whitelynx/dactyl-lynx-keyboard/things/dactyl-lynx-6x5-left-finger.stl

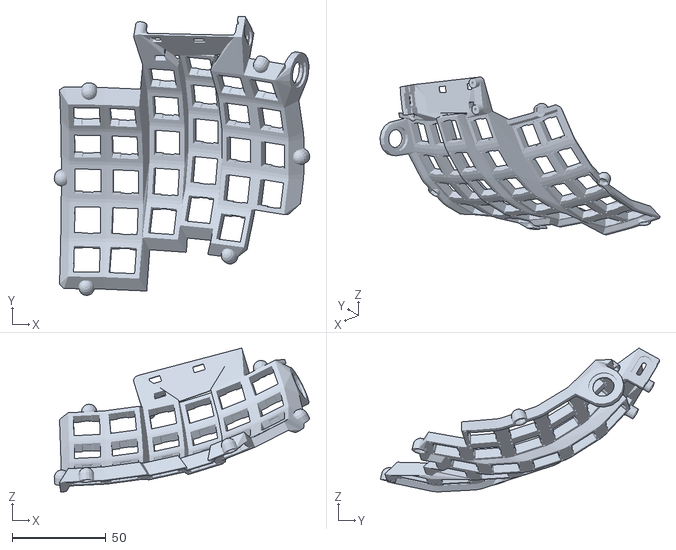
[picture p14: CAD file, 2024-12-01]
things/dactyl-lynx-6x5-left-finger.stl
136.0 x 148.5 x 76.6
