whitelynx/dactyl-lynx-keyboard/things/dactyl-lynx-6x5-left-bottom-with-feet-tripod.scad

include </home/whitelynx/.local/share/virtualenvs/dactyl-lynx-keyboard-vn24Ws0r/lib/python3.12/site-packages/solid2/extensions/bosl2/BOSL2/version.scad>;
include </home/whitelynx/.local/share/virtualenvs/dactyl-lynx-keyboard-vn24Ws0r/lib/python3.12/site-packages/solid2/extensions/bosl2/BOSL2/constants.scad>;
include </home/whitelynx/.local/share/virtualenvs/dactyl-lynx-keyboard-vn24Ws0r/lib/python3.12/site-packages/solid2/extensions/bosl2/BOSL2/transforms.scad>;
include </home/whitelynx/.local/share/virtualenvs/dactyl-lynx-keyboard-vn24Ws0r/lib/python3.12/site-packages/solid2/extensions/bosl2/BOSL2/distributors.scad>;
include </home/whitelynx/.local/share/virtualenvs/dactyl-lynx-keyboard-vn24Ws0r/lib/python3.12/site-packages/solid2/extensions/bosl2/BOSL2/mutators.scad>;
include </home/whitelynx/.local/share/virtualenvs/dactyl-lynx-keyboard-vn24Ws0r/lib/python3.12/site-packages/solid2/extensions/bosl2/BOSL2/color.scad>;
include </home/whitelynx/.local/share/virtualenvs/dactyl-lynx-keyboard-vn24Ws0r/lib/python3.12/site-packages/solid2/extensions/bosl2/BOSL2/attachments.scad>;
include </home/whitelynx/.local/share/virtualenvs/dactyl-lynx-keyboard-vn24Ws0r/lib/python3.12/site-packages/solid2/extensions/bosl2/BOSL2/shapes3d.scad>;
include </home/whitelynx/.local/share/virtualenvs/dactyl-lynx-keyboard-vn24Ws0r/lib/python3.12/site-packages/solid2/extensions/bosl2/BOSL2/shapes2d.scad>;
include </home/whitelynx/.local/share/virtualenvs/dactyl-lynx-keyboard-vn24Ws0r/lib/python3.12/site-packages/solid2/extensions/bosl2/BOSL2/drawing.scad>;
include </home/whitelynx/.local/share/virtualenvs/dactyl-lynx-keyboard-vn24Ws0r/lib/python3.12/site-packages/solid2/extensions/bosl2/BOSL2/masks3d.scad>;
include </home/whitelynx/.local/share/virtualenvs/dactyl-lynx-keyboard-vn24Ws0r/lib/python3.12/site-packages/solid2/extensions/bosl2/BOSL2/masks2d.scad>;
include </home/whitelynx/.local/share/virtualenvs/dactyl-lynx-keyboard-vn24Ws0r/lib/python3.12/site-packages/solid2/extensions/bosl2/BOSL2/math.scad>;
include </home/whitelynx/.local/share/virtualenvs/dactyl-lynx-keyboard-vn24Ws0r/lib/python3.12/site-packages/solid2/extensions/bosl2/BOSL2/paths.scad>;
include </home/whitelynx/.local/share/virtualenvs/dactyl-lynx-keyboard-vn24Ws0r/lib/python3.12/site-packages/solid2/extensions/bosl2/BOSL2/lists.scad>;
include </home/whitelynx/.local/share/virtualenvs/dactyl-lynx-keyboard-vn24Ws0r/lib/python3.12/site-packages/solid2/extensions/bosl2/BOSL2/comparisons.scad>;
include </home/whitelynx/.local/share/virtualenvs/dactyl-lynx-keyboard-vn24Ws0r/lib/python3.12/site-packages/solid2/extensions/bosl2/BOSL2/linalg.scad>;
include </home/whitelynx/.local/share/virtualenvs/dactyl-lynx-keyboard-vn24Ws0r/lib/python3.12/site-packages/solid2/extensions/bosl2/BOSL2/trigonometry.scad>;
include </home/whitelynx/.local/share/virtualenvs/dactyl-lynx-keyboard-vn24Ws0r/lib/python3.12/site-packages/solid2/extensions/bosl2/BOSL2/vectors.scad>;
include </home/whitelynx/.local/share/virtualenvs/dactyl-lynx-keyboard-vn24Ws0r/lib/python3.12/site-packages/solid2/extensions/bosl2/BOSL2/affine.scad>;
include </home/whitelynx/.local/share/virtualenvs/dactyl-lynx-keyboard-vn24Ws0r/lib/python3.12/site-packages/solid2/extensions/bosl2/BOSL2/coords.scad>;
include </home/whitelynx/.local/share/virtualenvs/dactyl-lynx-keyboard-vn24Ws0r/lib/python3.12/site-packages/solid2/extensions/bosl2/BOSL2/geometry.scad>;
include </home/whitelynx/.local/share/virtualenvs/dactyl-lynx-keyboard-vn24Ws0r/lib/python3.12/site-packages/solid2/extensions/bosl2/BOSL2/regions.scad>;
include </home/whitelynx/.local/share/virtualenvs/dactyl-lynx-keyboard-vn24Ws0r/lib/python3.12/site-packages/solid2/extensions/bosl2/BOSL2/strings.scad>;
include </home/whitelynx/.local/share/virtualenvs/dactyl-lynx-keyboard-vn24Ws0r/lib/python3.12/site-packages/solid2/extensions/bosl2/BOSL2/skin.scad>;
include </home/whitelynx/.local/share/virtualenvs/dactyl-lynx-keyboard-vn24Ws0r/lib/python3.12/site-packages/solid2/extensions/bosl2/BOSL2/vnf.scad>;
include </home/whitelynx/.local/share/virtualenvs/dactyl-lynx-keyboard-vn24Ws0r/lib/python3.12/site-packages/solid2/extensions/bosl2/BOSL2/utility.scad>;
include </home/whitelynx/.local/share/virtualenvs/dactyl-lynx-keyboard-vn24Ws0r/lib/python3.12/site-packages/solid2/extensions/bosl2/BOSL2/partitions.scad>;
include </home/whitelynx/.local/share/virtualenvs/dactyl-lynx-keyboard-vn24Ws0r/lib/python3.12/site-packages/solid2/extensions/bosl2/BOSL2/screws.scad>;

union() {
	mirror(v = [1, 0, 0]) {
		union() {
			difference() {
				union() {
					difference() {
						union() {
							translate(v = [0, 0, 30.5]) {
								rotate(a = 18.0, v = [1, 0, 0]) {
									rotate(a = 18.0, v = [0, 1, 0]) {
										translate(v = [0, 0, 3]) {
											translate(v = [0, 0, 230.49306344750678]) {
												rotate(a = 10.0, v = [0, 1, 0]) {
													translate(v = [0, 0, -230.49306344750678]) {
														translate(v = [0, 0, 79.73635378597841]) {
															rotate(a = 29.999999999999996, v = [1, 0, 0]) {
																translate(v = [0, 0, -79.73635378597841]) {
																	translate(v = [0, 0, -12.5]) {
																		cube(center = true, size = [20.0, 20.0, 3]);
																	}
																}
															}
														}
													}
												}
											}
										}
									}
								}
							}
							translate(v = [0, 0, 30.5]) {
								rotate(a = 18.0, v = [1, 0, 0]) {
									rotate(a = 18.0, v = [0, 1, 0]) {
										translate(v = [0, 0, 3]) {
											translate(v = [0, 0, 230.49306344750678]) {
												rotate(a = 5.0, v = [0, 1, 0]) {
													translate(v = [0, 0, -230.49306344750678]) {
														translate(v = [0, 0, 79.73635378597841]) {
															rotate(a = 29.999999999999996, v = [1, 0, 0]) {
																translate(v = [0, 0, -79.73635378597841]) {
																	translate(v = [-2, 0, -12.5]) {
																		cube(center = true, size = [20.0, 20.0, 3]);
																	}
																}
															}
														}
													}
												}
											}
										}
									}
								}
							}
							translate(v = [0, 0, 30.5]) {
								rotate(a = 18.0, v = [1, 0, 0]) {
									rotate(a = 18.0, v = [0, 1, 0]) {
										translate(v = [0, 0, 3]) {
											translate(v = [0, 6.82, -4.0]) {
												translate(v = [0, 0, 230.49306344750678]) {
													rotate(a = 0.0, v = [0, 1, 0]) {
														translate(v = [0, 0, -230.49306344750678]) {
															translate(v = [0, 0, 79.73635378597841]) {
																rotate(a = 29.999999999999996, v = [1, 0, 0]) {
																	translate(v = [0, 0, -79.73635378597841]) {
																		translate(v = [0, 0, -12.5]) {
																			cube(center = true, size = [22.0, 20.0, 3]);
																		}
																	}
																}
															}
														}
													}
												}
											}
										}
									}
								}
							}
							translate(v = [0, 0, 30.5]) {
								rotate(a = 18.0, v = [1, 0, 0]) {
									rotate(a = 18.0, v = [0, 1, 0]) {
										translate(v = [0, 0, 3]) {
											translate(v = [0, 0, 230.49306344750678]) {
												rotate(a = -5.0, v = [0, 1, 0]) {
													translate(v = [0, 0, -230.49306344750678]) {
														translate(v = [0, 0, 79.73635378597841]) {
															rotate(a = 29.999999999999996, v = [1, 0, 0]) {
																translate(v = [0, 0, -79.73635378597841]) {
																	translate(v = [2, 0, -12.5]) {
																		cube(center = true, size = [20.0, 20.0, 3]);
																	}
																}
															}
														}
													}
												}
											}
										}
									}
								}
							}
							translate(v = [0, 0, 30.5]) {
								rotate(a = 18.0, v = [1, 0, 0]) {
									rotate(a = 18.0, v = [0, 1, 0]) {
										translate(v = [0, 0, 3]) {
											translate(v = [0, -20.8, 7.64]) {
												translate(v = [0, 0, 230.49306344750678]) {
													rotate(a = -10.0, v = [0, 1, 0]) {
														translate(v = [0, 0, -230.49306344750678]) {
															translate(v = [0, 0, 79.73635378597841]) {
																rotate(a = 29.999999999999996, v = [1, 0, 0]) {
																	translate(v = [0, 0, -79.73635378597841]) {
																		translate(v = [2, 0, -12.5]) {
																			cube(center = true, size = [18.0, 20.0, 3]);
																		}
																	}
																}
															}
														}
													}
												}
											}
										}
									}
								}
							}
							translate(v = [0, 0, 30.5]) {
								rotate(a = 18.0, v = [1, 0, 0]) {
									rotate(a = 18.0, v = [0, 1, 0]) {
										translate(v = [0, 0, 3]) {
											translate(v = [0, -20.8, 7.64]) {
												translate(v = [0, 0, 230.49306344750678]) {
													rotate(a = -14.999999999999998, v = [0, 1, 0]) {
														translate(v = [0, 0, -230.49306344750678]) {
															translate(v = [0, 0, 79.73635378597841]) {
																rotate(a = 29.999999999999996, v = [1, 0, 0]) {
																	translate(v = [0, 0, -79.73635378597841]) {
																		translate(v = [0, 0, -12.5]) {
																			cube(center = true, size = [20.0, 20.0, 3]);
																		}
																	}
																}
															}
														}
													}
												}
											}
										}
									}
								}
							}
							translate(v = [0, 0, 30.5]) {
								rotate(a = 18.0, v = [1, 0, 0]) {
									rotate(a = 18.0, v = [0, 1, 0]) {
										translate(v = [0, 0, 3]) {
											translate(v = [0, 0, 230.49306344750678]) {
												rotate(a = 10.0, v = [0, 1, 0]) {
													translate(v = [0, 0, -230.49306344750678]) {
														translate(v = [0, 0, 79.73635378597841]) {
															rotate(a = 14.999999999999998, v = [1, 0, 0]) {
																translate(v = [0, 0, -79.73635378597841]) {
																	translate(v = [0, 0, -12.5]) {
																		cube(center = true, size = [20.0, 20.0, 3]);
																	}
																}
															}
														}
													}
												}
											}
										}
									}
								}
							}
							translate(v = [0, 0, 30.5]) {
								rotate(a = 18.0, v = [1, 0, 0]) {
									rotate(a = 18.0, v = [0, 1, 0]) {
										translate(v = [0, 0, 3]) {
											translate(v = [0, 0, 230.49306344750678]) {
												rotate(a = 5.0, v = [0, 1, 0]) {
													translate(v = [0, 0, -230.49306344750678]) {
														translate(v = [0, 0, 79.73635378597841]) {
															rotate(a = 14.999999999999998, v = [1, 0, 0]) {
																translate(v = [0, 0, -79.73635378597841]) {
																	translate(v = [-2, 0, -12.5]) {
																		cube(center = true, size = [20.0, 20.0, 3]);
																	}
																}
															}
														}
													}
												}
											}
										}
									}
								}
							}
							translate(v = [0, 0, 30.5]) {
								rotate(a = 18.0, v = [1, 0, 0]) {
									rotate(a = 18.0, v = [0, 1, 0]) {
										translate(v = [0, 0, 3]) {
											translate(v = [0, 6.82, -4.0]) {
												translate(v = [0, 0, 230.49306344750678]) {
													rotate(a = 0.0, v = [0, 1, 0]) {
														translate(v = [0, 0, -230.49306344750678]) {
															translate(v = [0, 0, 79.73635378597841]) {
																rotate(a = 14.999999999999998, v = [1, 0, 0]) {
																	translate(v = [0, 0, -79.73635378597841]) {
																		translate(v = [0, 0, -12.5]) {
																			cube(center = true, size = [22.0, 20.0, 3]);
																		}
																	}
																}
															}
														}
													}
												}
											}
										}
									}
								}
							}
							translate(v = [0, 0, 30.5]) {
								rotate(a = 18.0, v = [1, 0, 0]) {
									rotate(a = 18.0, v = [0, 1, 0]) {
										translate(v = [0, 0, 3]) {
											translate(v = [0, 0, 230.49306344750678]) {
												rotate(a = -5.0, v = [0, 1, 0]) {
													translate(v = [0, 0, -230.49306344750678]) {
														translate(v = [0, 0, 79.73635378597841]) {
															rotate(a = 14.999999999999998, v = [1, 0, 0]) {
																translate(v = [0, 0, -79.73635378597841]) {
																	translate(v = [2, 0, -12.5]) {
																		cube(center = true, size = [20.0, 20.0, 3]);
																	}
																}
															}
														}
													}
												}
											}
										}
									}
								}
							}
							translate(v = [0, 0, 30.5]) {
								rotate(a = 18.0, v = [1, 0, 0]) {
									rotate(a = 18.0, v = [0, 1, 0]) {
										translate(v = [0, 0, 3]) {
											translate(v = [0, -20.8, 7.64]) {
												translate(v = [0, 0, 230.49306344750678]) {
													rotate(a = -10.0, v = [0, 1, 0]) {
														translate(v = [0, 0, -230.49306344750678]) {
															translate(v = [0, 0, 79.73635378597841]) {
																rotate(a = 14.999999999999998, v = [1, 0, 0]) {
																	translate(v = [0, 0, -79.73635378597841]) {
																		translate(v = [2, 0, -12.5]) {
																			cube(center = true, size = [18.0, 20.0, 3]);
																		}
																	}
																}
															}
														}
													}
												}
											}
										}
									}
								}
							}
							translate(v = [0, 0, 30.5]) {
								rotate(a = 18.0, v = [1, 0, 0]) {
									rotate(a = 18.0, v = [0, 1, 0]) {
										translate(v = [0, 0, 3]) {
											translate(v = [0, -20.8, 7.64]) {
												translate(v = [0, 0, 230.49306344750678]) {
													rotate(a = -14.999999999999998, v = [0, 1, 0]) {
														translate(v = [0, 0, -230.49306344750678]) {
															translate(v = [0, 0, 79.73635378597841]) {
																rotate(a = 14.999999999999998, v = [1, 0, 0]) {
																	translate(v = [0, 0, -79.73635378597841]) {
																		translate(v = [0, 0, -12.5]) {
																			cube(center = true, size = [20.0, 20.0, 3]);
																		}
																	}
																}
															}
														}
													}
												}
											}
										}
									}
								}
							}
							translate(v = [0, 0, 30.5]) {
								rotate(a = 18.0, v = [1, 0, 0]) {
									rotate(a = 18.0, v = [0, 1, 0]) {
										translate(v = [0, 0, 3]) {
											translate(v = [0, 0, 230.49306344750678]) {
												rotate(a = 10.0, v = [0, 1, 0]) {
													translate(v = [0, 0, -230.49306344750678]) {
														translate(v = [0, 0, 79.73635378597841]) {
															rotate(a = 0.0, v = [1, 0, 0]) {
																translate(v = [0, 0, -79.73635378597841]) {
																	translate(v = [0, 0, -12.5]) {
																		cube(center = true, size = [20.0, 20.0, 3]);
																	}
																}
															}
														}
													}
												}
											}
										}
									}
								}
							}
							translate(v = [0, 0, 30.5]) {
								rotate(a = 18.0, v = [1, 0, 0]) {
									rotate(a = 18.0, v = [0, 1, 0]) {
										translate(v = [0, 0, 3]) {
											translate(v = [0, 0, 230.49306344750678]) {
												rotate(a = 5.0, v = [0, 1, 0]) {
													translate(v = [0, 0, -230.49306344750678]) {
														translate(v = [0, 0, 79.73635378597841]) {
															rotate(a = 0.0, v = [1, 0, 0]) {
																translate(v = [0, 0, -79.73635378597841]) {
																	translate(v = [-2, 0, -12.5]) {
																		cube(center = true, size = [20.0, 20.0, 3]);
																	}
																}
															}
														}
													}
												}
											}
										}
									}
								}
							}
							translate(v = [0, 0, 30.5]) {
								rotate(a = 18.0, v = [1, 0, 0]) {
									rotate(a = 18.0, v = [0, 1, 0]) {
										translate(v = [0, 0, 3]) {
											translate(v = [0, 6.82, -4.0]) {
												translate(v = [0, 0, 230.49306344750678]) {
													rotate(a = 0.0, v = [0, 1, 0]) {
														translate(v = [0, 0, -230.49306344750678]) {
															translate(v = [0, 0, 79.73635378597841]) {
																rotate(a = 0.0, v = [1, 0, 0]) {
																	translate(v = [0, 0, -79.73635378597841]) {
																		translate(v = [0, 0, -12.5]) {
																			cube(center = true, size = [22.0, 20.0, 3]);
																		}
																	}
																}
															}
														}
													}
												}
											}
										}
									}
								}
							}
							translate(v = [0, 0, 30.5]) {
								rotate(a = 18.0, v = [1, 0, 0]) {
									rotate(a = 18.0, v = [0, 1, 0]) {
										translate(v = [0, 0, 3]) {
											translate(v = [0, 0, 230.49306344750678]) {
												rotate(a = -5.0, v = [0, 1, 0]) {
													translate(v = [0, 0, -230.49306344750678]) {
														translate(v = [0, 0, 79.73635378597841]) {
															rotate(a = 0.0, v = [1, 0, 0]) {
																translate(v = [0, 0, -79.73635378597841]) {
																	translate(v = [2, 0, -12.5]) {
																		cube(center = true, size = [20.0, 20.0, 3]);
																	}
																}
															}
														}
													}
												}
											}
										}
									}
								}
							}
							translate(v = [0, 0, 30.5]) {
								rotate(a = 18.0, v = [1, 0, 0]) {
									rotate(a = 18.0, v = [0, 1, 0]) {
										translate(v = [0, 0, 3]) {
											translate(v = [0, -20.8, 7.64]) {
												translate(v = [0, 0, 230.49306344750678]) {
													rotate(a = -10.0, v = [0, 1, 0]) {
														translate(v = [0, 0, -230.49306344750678]) {
															translate(v = [0, 0, 79.73635378597841]) {
																rotate(a = 0.0, v = [1, 0, 0]) {
																	translate(v = [0, 0, -79.73635378597841]) {
																		translate(v = [2, 0, -12.5]) {
																			cube(center = true, size = [18.0, 20.0, 3]);
																		}
																	}
																}
															}
														}
													}
												}
											}
										}
									}
								}
							}
							translate(v = [0, 0, 30.5]) {
								rotate(a = 18.0, v = [1, 0, 0]) {
									rotate(a = 18.0, v = [0, 1, 0]) {
										translate(v = [0, 0, 3]) {
											translate(v = [0, -20.8, 7.64]) {
												translate(v = [0, 0, 230.49306344750678]) {
													rotate(a = -14.999999999999998, v = [0, 1, 0]) {
														translate(v = [0, 0, -230.49306344750678]) {
															translate(v = [0, 0, 79.73635378597841]) {
																rotate(a = 0.0, v = [1, 0, 0]) {
																	translate(v = [0, 0, -79.73635378597841]) {
																		translate(v = [0, 0, -12.5]) {
																			cube(center = true, size = [20.0, 20.0, 3]);
																		}
																	}
																}
															}
														}
													}
												}
											}
										}
									}
								}
							}
							translate(v = [0, 0, 30.5]) {
								rotate(a = 18.0, v = [1, 0, 0]) {
									rotate(a = 18.0, v = [0, 1, 0]) {
										translate(v = [0, 0, 3]) {
											translate(v = [0, 0, 230.49306344750678]) {
												rotate(a = 10.0, v = [0, 1, 0]) {
													translate(v = [0, 0, -230.49306344750678]) {
														translate(v = [0, 0, 79.73635378597841]) {
															rotate(a = -14.999999999999998, v = [1, 0, 0]) {
																translate(v = [0, 0, -79.73635378597841]) {
																	translate(v = [0, 0, -12.5]) {
																		cube(center = true, size = [20.0, 20.0, 3]);
																	}
																}
															}
														}
													}
												}
											}
										}
									}
								}
							}
							translate(v = [0, 0, 30.5]) {
								rotate(a = 18.0, v = [1, 0, 0]) {
									rotate(a = 18.0, v = [0, 1, 0]) {
										translate(v = [0, 0, 3]) {
											translate(v = [0, 0, 230.49306344750678]) {
												rotate(a = 5.0, v = [0, 1, 0]) {
													translate(v = [0, 0, -230.49306344750678]) {
														translate(v = [0, 0, 79.73635378597841]) {
															rotate(a = -14.999999999999998, v = [1, 0, 0]) {
																translate(v = [0, 0, -79.73635378597841]) {
																	translate(v = [-2, 0, -12.5]) {
																		cube(center = true, size = [20.0, 20.0, 3]);
																	}
																}
															}
														}
													}
												}
											}
										}
									}
								}
							}
							translate(v = [0, 0, 30.5]) {
								rotate(a = 18.0, v = [1, 0, 0]) {
									rotate(a = 18.0, v = [0, 1, 0]) {
										translate(v = [0, 0, 3]) {
											translate(v = [0, 6.82, -4.0]) {
												translate(v = [0, 0, 230.49306344750678]) {
													rotate(a = 0.0, v = [0, 1, 0]) {
														translate(v = [0, 0, -230.49306344750678]) {
															translate(v = [0, 0, 79.73635378597841]) {
																rotate(a = -14.999999999999998, v = [1, 0, 0]) {
																	translate(v = [0, 0, -79.73635378597841]) {
																		translate(v = [0, 0, -12.5]) {
																			cube(center = true, size = [22.0, 20.0, 3]);
																		}
																	}
																}
															}
														}
													}
												}
											}
										}
									}
								}
							}
							translate(v = [0, 0, 30.5]) {
								rotate(a = 18.0, v = [1, 0, 0]) {
									rotate(a = 18.0, v = [0, 1, 0]) {
										translate(v = [0, 0, 3]) {
											translate(v = [0, 0, 230.49306344750678]) {
												rotate(a = -5.0, v = [0, 1, 0]) {
													translate(v = [0, 0, -230.49306344750678]) {
														translate(v = [0, 0, 79.73635378597841]) {
															rotate(a = -14.999999999999998, v = [1, 0, 0]) {
																translate(v = [0, 0, -79.73635378597841]) {
																	translate(v = [2, 0, -12.5]) {
																		cube(center = true, size = [20.0, 20.0, 3]);
																	}
																}
															}
														}
													}
												}
											}
										}
									}
								}
							}
							translate(v = [0, 0, 30.5]) {
								rotate(a = 18.0, v = [1, 0, 0]) {
									rotate(a = 18.0, v = [0, 1, 0]) {
										translate(v = [0, 0, 3]) {
											translate(v = [0, -20.8, 7.64]) {
												translate(v = [0, 0, 230.49306344750678]) {
													rotate(a = -10.0, v = [0, 1, 0]) {
														translate(v = [0, 0, -230.49306344750678]) {
															translate(v = [0, 0, 79.73635378597841]) {
																rotate(a = -14.999999999999998, v = [1, 0, 0]) {
																	translate(v = [0, 0, -79.73635378597841]) {
																		translate(v = [2, 0, -12.5]) {
																			cube(center = true, size = [18.0, 20.0, 3]);
																		}
																	}
																}
															}
														}
													}
												}
											}
										}
									}
								}
							}
							translate(v = [0, 0, 30.5]) {
								rotate(a = 18.0, v = [1, 0, 0]) {
									rotate(a = 18.0, v = [0, 1, 0]) {
										translate(v = [0, 0, 3]) {
											translate(v = [0, -20.8, 7.64]) {
												translate(v = [0, 0, 230.49306344750678]) {
													rotate(a = -14.999999999999998, v = [0, 1, 0]) {
														translate(v = [0, 0, -230.49306344750678]) {
															translate(v = [0, 0, 79.73635378597841]) {
																rotate(a = -14.999999999999998, v = [1, 0, 0]) {
																	translate(v = [0, 0, -79.73635378597841]) {
																		translate(v = [0, 0, -12.5]) {
																			cube(center = true, size = [20.0, 20.0, 3]);
																		}
																	}
																}
															}
														}
													}
												}
											}
										}
									}
								}
							}
							translate(v = [0, 0, 30.5]) {
								rotate(a = 18.0, v = [1, 0, 0]) {
									rotate(a = 18.0, v = [0, 1, 0]) {
										translate(v = [0, 0, 3]) {
											translate(v = [0, 0, 230.49306344750678]) {
												rotate(a = 5.0, v = [0, 1, 0]) {
													translate(v = [0, 0, -230.49306344750678]) {
														translate(v = [0, 0, 79.73635378597841]) {
															rotate(a = -29.999999999999996, v = [1, 0, 0]) {
																translate(v = [0, 0, -79.73635378597841]) {
																	translate(v = [-2, 0, -12.5]) {
																		cube(center = true, size = [20.0, 20.0, 3]);
																	}
																}
															}
														}
													}
												}
											}
										}
									}
								}
							}
							translate(v = [0, 0, 30.5]) {
								rotate(a = 18.0, v = [1, 0, 0]) {
									rotate(a = 18.0, v = [0, 1, 0]) {
										translate(v = [0, 0, 3]) {
											translate(v = [0, 6.82, -4.0]) {
												translate(v = [0, 0, 230.49306344750678]) {
													rotate(a = 0.0, v = [0, 1, 0]) {
														translate(v = [0, 0, -230.49306344750678]) {
															translate(v = [0, 0, 79.73635378597841]) {
																rotate(a = -29.999999999999996, v = [1, 0, 0]) {
																	translate(v = [0, 0, -79.73635378597841]) {
																		translate(v = [0, 0, -12.5]) {
																			cube(center = true, size = [22.0, 20.0, 3]);
																		}
																	}
																}
															}
														}
													}
												}
											}
										}
									}
								}
							}
							translate(v = [0, 0, 30.5]) {
								rotate(a = 18.0, v = [1, 0, 0]) {
									rotate(a = 18.0, v = [0, 1, 0]) {
										translate(v = [0, 0, 3]) {
											translate(v = [0, 0, 230.49306344750678]) {
												rotate(a = -5.0, v = [0, 1, 0]) {
													translate(v = [0, 0, -230.49306344750678]) {
														translate(v = [0, 0, 79.73635378597841]) {
															rotate(a = -29.999999999999996, v = [1, 0, 0]) {
																translate(v = [0, 0, -79.73635378597841]) {
																	translate(v = [2, 0, -12.5]) {
																		cube(center = true, size = [20.0, 20.0, 3]);
																	}
																}
															}
														}
													}
												}
											}
										}
									}
								}
							}
							translate(v = [0, 0, 30.5]) {
								rotate(a = 18.0, v = [1, 0, 0]) {
									rotate(a = 18.0, v = [0, 1, 0]) {
										translate(v = [0, 0, 3]) {
											translate(v = [0, -20.8, 7.64]) {
												translate(v = [0, 0, 230.49306344750678]) {
													rotate(a = -10.0, v = [0, 1, 0]) {
														translate(v = [0, 0, -230.49306344750678]) {
															translate(v = [0, 0, 79.73635378597841]) {
																rotate(a = -29.999999999999996, v = [1, 0, 0]) {
																	translate(v = [0, 0, -79.73635378597841]) {
																		translate(v = [2, 0, -12.5]) {
																			cube(center = true, size = [18.0, 20.0, 3]);
																		}
																	}
																}
															}
														}
													}
												}
											}
										}
									}
								}
							}
							translate(v = [0, 0, 30.5]) {
								rotate(a = 18.0, v = [1, 0, 0]) {
									rotate(a = 18.0, v = [0, 1, 0]) {
										translate(v = [0, 0, 3]) {
											translate(v = [0, -20.8, 7.64]) {
												translate(v = [0, 0, 230.49306344750678]) {
													rotate(a = -14.999999999999998, v = [0, 1, 0]) {
														translate(v = [0, 0, -230.49306344750678]) {
															translate(v = [0, 0, 79.73635378597841]) {
																rotate(a = -29.999999999999996, v = [1, 0, 0]) {
																	translate(v = [0, 0, -79.73635378597841]) {
																		translate(v = [0, 0, -12.5]) {
																			cube(center = true, size = [20.0, 20.0, 3]);
																		}
																	}
																}
															}
														}
													}
												}
											}
										}
									}
								}
							}
							hull() {
								translate(v = [0, 0, 30.5]) {
									rotate(a = 18.0, v = [1, 0, 0]) {
										rotate(a = 18.0, v = [0, 1, 0]) {
											translate(v = [0, 0, 3]) {
												translate(v = [0, 0, 230.49306344750678]) {
													rotate(a = 5.0, v = [0, 1, 0]) {
														translate(v = [0, 0, -230.49306344750678]) {
															translate(v = [0, 0, 79.73635378597841]) {
																rotate(a = 14.999999999999998, v = [1, 0, 0]) {
																	translate(v = [0, 0, -79.73635378597841]) {
																		translate(v = [-11.95, 9.95, -11]) {
																			translate(v = [0, 0, -1.5]) {
																				cube(center = true, size = [0.1, 0.1, 3]);
																			}
																		}
																	}
																}
															}
														}
													}
												}
											}
										}
									}
								}
								translate(v = [0, 0, 30.5]) {
									rotate(a = 18.0, v = [1, 0, 0]) {
										rotate(a = 18.0, v = [0, 1, 0]) {
											translate(v = [0, 0, 3]) {
												translate(v = [0, 0, 230.49306344750678]) {
													rotate(a = 10.0, v = [0, 1, 0]) {
														translate(v = [0, 0, -230.49306344750678]) {
															translate(v = [0, 0, 79.73635378597841]) {
																rotate(a = 14.999999999999998, v = [1, 0, 0]) {
																	translate(v = [0, 0, -79.73635378597841]) {
																		translate(v = [9.95, 9.95, -11]) {
																			translate(v = [0, 0, -1.5]) {
																				cube(center = true, size = [0.1, 0.1, 3]);
																			}
																		}
																	}
																}
															}
														}
													}
												}
											}
										}
									}
								}
								translate(v = [0, 0, 30.5]) {
									rotate(a = 18.0, v = [1, 0, 0]) {
										rotate(a = 18.0, v = [0, 1, 0]) {
											translate(v = [0, 0, 3]) {
												translate(v = [0, 0, 230.49306344750678]) {
													rotate(a = 10.0, v = [0, 1, 0]) {
														translate(v = [0, 0, -230.49306344750678]) {
															translate(v = [0, 0, 79.73635378597841]) {
																rotate(a = 29.999999999999996, v = [1, 0, 0]) {
																	translate(v = [0, 0, -79.73635378597841]) {
																		translate(v = [9.95, -9.95, -11]) {
																			translate(v = [0, 0, -1.5]) {
																				cube(center = true, size = [0.1, 0.1, 3]);
																			}
																		}
																	}
																}
															}
														}
													}
												}
											}
										}
									}
								}
								translate(v = [0, 0, 30.5]) {
									rotate(a = 18.0, v = [1, 0, 0]) {
										rotate(a = 18.0, v = [0, 1, 0]) {
											translate(v = [0, 0, 3]) {
												translate(v = [0, 0, 230.49306344750678]) {
													rotate(a = 5.0, v = [0, 1, 0]) {
														translate(v = [0, 0, -230.49306344750678]) {
															translate(v = [0, 0, 79.73635378597841]) {
																rotate(a = 29.999999999999996, v = [1, 0, 0]) {
																	translate(v = [0, 0, -79.73635378597841]) {
																		translate(v = [-11.95, -9.95, -11]) {
																			translate(v = [0, 0, -1.5]) {
																				cube(center = true, size = [0.1, 0.1, 3]);
																			}
																		}
																	}
																}
															}
														}
													}
												}
											}
										}
									}
								}
							}
							hull() {
								translate(v = [0, 0, 30.5]) {
									rotate(a = 18.0, v = [1, 0, 0]) {
										rotate(a = 18.0, v = [0, 1, 0]) {
											translate(v = [0, 0, 3]) {
												translate(v = [0, 6.82, -4.0]) {
													translate(v = [0, 0, 230.49306344750678]) {
														rotate(a = 0.0, v = [0, 1, 0]) {
															translate(v = [0, 0, -230.49306344750678]) {
																translate(v = [0, 0, 79.73635378597841]) {
																	rotate(a = 14.999999999999998, v = [1, 0, 0]) {
																		translate(v = [0, 0, -79.73635378597841]) {
																			translate(v = [-10.95, 9.95, -11]) {
																				translate(v = [0, 0, -1.5]) {
																					cube(center = true, size = [0.1, 0.1, 3]);
																				}
																			}
																		}
																	}
																}
															}
														}
													}
												}
											}
										}
									}
								}
								translate(v = [0, 0, 30.5]) {
									rotate(a = 18.0, v = [1, 0, 0]) {
										rotate(a = 18.0, v = [0, 1, 0]) {
											translate(v = [0, 0, 3]) {
												translate(v = [0, 0, 230.49306344750678]) {
													rotate(a = 5.0, v = [0, 1, 0]) {
														translate(v = [0, 0, -230.49306344750678]) {
															translate(v = [0, 0, 79.73635378597841]) {
																rotate(a = 14.999999999999998, v = [1, 0, 0]) {
																	translate(v = [0, 0, -79.73635378597841]) {
																		translate(v = [7.949999999999999, 9.95, -11]) {
																			translate(v = [0, 0, -1.5]) {
																				cube(center = true, size = [0.1, 0.1, 3]);
																			}
																		}
																	}
																}
															}
														}
													}
												}
											}
										}
									}
								}
								translate(v = [0, 0, 30.5]) {
									rotate(a = 18.0, v = [1, 0, 0]) {
										rotate(a = 18.0, v = [0, 1, 0]) {
											translate(v = [0, 0, 3]) {
												translate(v = [0, 0, 230.49306344750678]) {
													rotate(a = 5.0, v = [0, 1, 0]) {
														translate(v = [0, 0, -230.49306344750678]) {
															translate(v = [0, 0, 79.73635378597841]) {
																rotate(a = 29.999999999999996, v = [1, 0, 0]) {
																	translate(v = [0, 0, -79.73635378597841]) {
																		translate(v = [7.949999999999999, -9.95, -11]) {
																			translate(v = [0, 0, -1.5]) {
																				cube(center = true, size = [0.1, 0.1, 3]);
																			}
																		}
																	}
																}
															}
														}
													}
												}
											}
										}
									}
								}
								translate(v = [0, 0, 30.5]) {
									rotate(a = 18.0, v = [1, 0, 0]) {
										rotate(a = 18.0, v = [0, 1, 0]) {
											translate(v = [0, 0, 3]) {
												translate(v = [0, 6.82, -4.0]) {
													translate(v = [0, 0, 230.49306344750678]) {
														rotate(a = 0.0, v = [0, 1, 0]) {
															translate(v = [0, 0, -230.49306344750678]) {
																translate(v = [0, 0, 79.73635378597841]) {
																	rotate(a = 29.999999999999996, v = [1, 0, 0]) {
																		translate(v = [0, 0, -79.73635378597841]) {
																			translate(v = [-10.95, -9.95, -11]) {
																				translate(v = [0, 0, -1.5]) {
																					cube(center = true, size = [0.1, 0.1, 3]);
																				}
																			}
																		}
																	}
																}
															}
														}
													}
												}
											}
										}
									}
								}
							}
							hull() {
								translate(v = [0, 0, 30.5]) {
									rotate(a = 18.0, v = [1, 0, 0]) {
										rotate(a = 18.0, v = [0, 1, 0]) {
											translate(v = [0, 0, 3]) {
												translate(v = [0, 0, 230.49306344750678]) {
													rotate(a = -5.0, v = [0, 1, 0]) {
														translate(v = [0, 0, -230.49306344750678]) {
															translate(v = [0, 0, 79.73635378597841]) {
																rotate(a = 14.999999999999998, v = [1, 0, 0]) {
																	translate(v = [0, 0, -79.73635378597841]) {
																		translate(v = [-7.949999999999999, 9.95, -11]) {
																			translate(v = [0, 0, -1.5]) {
																				cube(center = true, size = [0.1, 0.1, 3]);
																			}
																		}
																	}
																}
															}
														}
													}
												}
											}
										}
									}
								}
								translate(v = [0, 0, 30.5]) {
									rotate(a = 18.0, v = [1, 0, 0]) {
										rotate(a = 18.0, v = [0, 1, 0]) {
											translate(v = [0, 0, 3]) {
												translate(v = [0, 6.82, -4.0]) {
													translate(v = [0, 0, 230.49306344750678]) {
														rotate(a = 0.0, v = [0, 1, 0]) {
															translate(v = [0, 0, -230.49306344750678]) {
																translate(v = [0, 0, 79.73635378597841]) {
																	rotate(a = 14.999999999999998, v = [1, 0, 0]) {
																		translate(v = [0, 0, -79.73635378597841]) {
																			translate(v = [10.95, 9.95, -11]) {
																				translate(v = [0, 0, -1.5]) {
																					cube(center = true, size = [0.1, 0.1, 3]);
																				}
																			}
																		}
																	}
																}
															}
														}
													}
												}
											}
										}
									}
								}
								translate(v = [0, 0, 30.5]) {
									rotate(a = 18.0, v = [1, 0, 0]) {
										rotate(a = 18.0, v = [0, 1, 0]) {
											translate(v = [0, 0, 3]) {
												translate(v = [0, 6.82, -4.0]) {
													translate(v = [0, 0, 230.49306344750678]) {
														rotate(a = 0.0, v = [0, 1, 0]) {
															translate(v = [0, 0, -230.49306344750678]) {
																translate(v = [0, 0, 79.73635378597841]) {
																	rotate(a = 29.999999999999996, v = [1, 0, 0]) {
																		translate(v = [0, 0, -79.73635378597841]) {
																			translate(v = [10.95, -9.95, -11]) {
																				translate(v = [0, 0, -1.5]) {
																					cube(center = true, size = [0.1, 0.1, 3]);
																				}
																			}
																		}
																	}
																}
															}
														}
													}
												}
											}
										}
									}
								}
								translate(v = [0, 0, 30.5]) {
									rotate(a = 18.0, v = [1, 0, 0]) {
										rotate(a = 18.0, v = [0, 1, 0]) {
											translate(v = [0, 0, 3]) {
												translate(v = [0, 0, 230.49306344750678]) {
													rotate(a = -5.0, v = [0, 1, 0]) {
														translate(v = [0, 0, -230.49306344750678]) {
															translate(v = [0, 0, 79.73635378597841]) {
																rotate(a = 29.999999999999996, v = [1, 0, 0]) {
																	translate(v = [0, 0, -79.73635378597841]) {
																		translate(v = [-7.949999999999999, -9.95, -11]) {
																			translate(v = [0, 0, -1.5]) {
																				cube(center = true, size = [0.1, 0.1, 3]);
																			}
																		}
																	}
																}
															}
														}
													}
												}
											}
										}
									}
								}
							}
							hull() {
								translate(v = [0, 0, 30.5]) {
									rotate(a = 18.0, v = [1, 0, 0]) {
										rotate(a = 18.0, v = [0, 1, 0]) {
											translate(v = [0, 0, 3]) {
												translate(v = [0, -20.8, 7.64]) {
													translate(v = [0, 0, 230.49306344750678]) {
														rotate(a = -10.0, v = [0, 1, 0]) {
															translate(v = [0, 0, -230.49306344750678]) {
																translate(v = [0, 0, 79.73635378597841]) {
																	rotate(a = 14.999999999999998, v = [1, 0, 0]) {
																		translate(v = [0, 0, -79.73635378597841]) {
																			translate(v = [-6.949999999999999, 9.95, -11]) {
																				translate(v = [0, 0, -1.5]) {
																					cube(center = true, size = [0.1, 0.1, 3]);
																				}
																			}
																		}
																	}
																}
															}
														}
													}
												}
											}
										}
									}
								}
								translate(v = [0, 0, 30.5]) {
									rotate(a = 18.0, v = [1, 0, 0]) {
										rotate(a = 18.0, v = [0, 1, 0]) {
											translate(v = [0, 0, 3]) {
												translate(v = [0, 0, 230.49306344750678]) {
													rotate(a = -5.0, v = [0, 1, 0]) {
														translate(v = [0, 0, -230.49306344750678]) {
															translate(v = [0, 0, 79.73635378597841]) {
																rotate(a = 14.999999999999998, v = [1, 0, 0]) {
																	translate(v = [0, 0, -79.73635378597841]) {
																		translate(v = [11.95, 9.95, -11]) {
																			translate(v = [0, 0, -1.5]) {
																				cube(center = true, size = [0.1, 0.1, 3]);
																			}
																		}
																	}
																}
															}
														}
													}
												}
											}
										}
									}
								}
								translate(v = [0, 0, 30.5]) {
									rotate(a = 18.0, v = [1, 0, 0]) {
										rotate(a = 18.0, v = [0, 1, 0]) {
											translate(v = [0, 0, 3]) {
												translate(v = [0, 0, 230.49306344750678]) {
													rotate(a = -5.0, v = [0, 1, 0]) {
														translate(v = [0, 0, -230.49306344750678]) {
															translate(v = [0, 0, 79.73635378597841]) {
																rotate(a = 29.999999999999996, v = [1, 0, 0]) {
																	translate(v = [0, 0, -79.73635378597841]) {
																		translate(v = [11.95, -9.95, -11]) {
																			translate(v = [0, 0, -1.5]) {
																				cube(center = true, size = [0.1, 0.1, 3]);
																			}
																		}
																	}
																}
															}
														}
													}
												}
											}
										}
									}
								}
								translate(v = [0, 0, 30.5]) {
									rotate(a = 18.0, v = [1, 0, 0]) {
										rotate(a = 18.0, v = [0, 1, 0]) {
											translate(v = [0, 0, 3]) {
												translate(v = [0, -20.8, 7.64]) {
													translate(v = [0, 0, 230.49306344750678]) {
														rotate(a = -10.0, v = [0, 1, 0]) {
															translate(v = [0, 0, -230.49306344750678]) {
																translate(v = [0, 0, 79.73635378597841]) {
																	rotate(a = 29.999999999999996, v = [1, 0, 0]) {
																		translate(v = [0, 0, -79.73635378597841]) {
																			translate(v = [-6.949999999999999, -9.95, -11]) {
																				translate(v = [0, 0, -1.5]) {
																					cube(center = true, size = [0.1, 0.1, 3]);
																				}
																			}
																		}
																	}
																}
															}
														}
													}
												}
											}
										}
									}
								}
							}
							hull() {
								translate(v = [0, 0, 30.5]) {
									rotate(a = 18.0, v = [1, 0, 0]) {
										rotate(a = 18.0, v = [0, 1, 0]) {
											translate(v = [0, 0, 3]) {
												translate(v = [0, -20.8, 7.64]) {
													translate(v = [0, 0, 230.49306344750678]) {
														rotate(a = -14.999999999999998, v = [0, 1, 0]) {
															translate(v = [0, 0, -230.49306344750678]) {
																translate(v = [0, 0, 79.73635378597841]) {
																	rotate(a = 14.999999999999998, v = [1, 0, 0]) {
																		translate(v = [0, 0, -79.73635378597841]) {
																			translate(v = [-9.95, 9.95, -11]) {
																				translate(v = [0, 0, -1.5]) {
																					cube(center = true, size = [0.1, 0.1, 3]);
																				}
																			}
																		}
																	}
																}
															}
														}
													}
												}
											}
										}
									}
								}
								translate(v = [0, 0, 30.5]) {
									rotate(a = 18.0, v = [1, 0, 0]) {
										rotate(a = 18.0, v = [0, 1, 0]) {
											translate(v = [0, 0, 3]) {
												translate(v = [0, -20.8, 7.64]) {
													translate(v = [0, 0, 230.49306344750678]) {
														rotate(a = -10.0, v = [0, 1, 0]) {
															translate(v = [0, 0, -230.49306344750678]) {
																translate(v = [0, 0, 79.73635378597841]) {
																	rotate(a = 14.999999999999998, v = [1, 0, 0]) {
																		translate(v = [0, 0, -79.73635378597841]) {
																			translate(v = [10.95, 9.95, -11]) {
																				translate(v = [0, 0, -1.5]) {
																					cube(center = true, size = [0.1, 0.1, 3]);
																				}
																			}
																		}
																	}
																}
															}
														}
													}
												}
											}
										}
									}
								}
								translate(v = [0, 0, 30.5]) {
									rotate(a = 18.0, v = [1, 0, 0]) {
										rotate(a = 18.0, v = [0, 1, 0]) {
											translate(v = [0, 0, 3]) {
												translate(v = [0, -20.8, 7.64]) {
													translate(v = [0, 0, 230.49306344750678]) {
														rotate(a = -10.0, v = [0, 1, 0]) {
															translate(v = [0, 0, -230.49306344750678]) {
																translate(v = [0, 0, 79.73635378597841]) {
																	rotate(a = 29.999999999999996, v = [1, 0, 0]) {
																		translate(v = [0, 0, -79.73635378597841]) {
																			translate(v = [10.95, -9.95, -11]) {
																				translate(v = [0, 0, -1.5]) {
																					cube(center = true, size = [0.1, 0.1, 3]);
																				}
																			}
																		}
																	}
																}
															}
														}
													}
												}
											}
										}
									}
								}
								translate(v = [0, 0, 30.5]) {
									rotate(a = 18.0, v = [1, 0, 0]) {
										rotate(a = 18.0, v = [0, 1, 0]) {
											translate(v = [0, 0, 3]) {
												translate(v = [0, -20.8, 7.64]) {
													translate(v = [0, 0, 230.49306344750678]) {
														rotate(a = -14.999999999999998, v = [0, 1, 0]) {
															translate(v = [0, 0, -230.49306344750678]) {
																translate(v = [0, 0, 79.73635378597841]) {
																	rotate(a = 29.999999999999996, v = [1, 0, 0]) {
																		translate(v = [0, 0, -79.73635378597841]) {
																			translate(v = [-9.95, -9.95, -11]) {
																				translate(v = [0, 0, -1.5]) {
																					cube(center = true, size = [0.1, 0.1, 3]);
																				}
																			}
																		}
																	}
																}
															}
														}
													}
												}
											}
										}
									}
								}
							}
							hull() {
								translate(v = [0, 0, 30.5]) {
									rotate(a = 18.0, v = [1, 0, 0]) {
										rotate(a = 18.0, v = [0, 1, 0]) {
											translate(v = [0, 0, 3]) {
												translate(v = [0, 0, 230.49306344750678]) {
													rotate(a = 5.0, v = [0, 1, 0]) {
														translate(v = [0, 0, -230.49306344750678]) {
															translate(v = [0, 0, 79.73635378597841]) {
																rotate(a = 0.0, v = [1, 0, 0]) {
																	translate(v = [0, 0, -79.73635378597841]) {
																		translate(v = [-11.95, 9.95, -11]) {
																			translate(v = [0, 0, -1.5]) {
																				cube(center = true, size = [0.1, 0.1, 3]);
																			}
																		}
																	}
																}
															}
														}
													}
												}
											}
										}
									}
								}
								translate(v = [0, 0, 30.5]) {
									rotate(a = 18.0, v = [1, 0, 0]) {
										rotate(a = 18.0, v = [0, 1, 0]) {
											translate(v = [0, 0, 3]) {
												translate(v = [0, 0, 230.49306344750678]) {
													rotate(a = 10.0, v = [0, 1, 0]) {
														translate(v = [0, 0, -230.49306344750678]) {
															translate(v = [0, 0, 79.73635378597841]) {
																rotate(a = 0.0, v = [1, 0, 0]) {
																	translate(v = [0, 0, -79.73635378597841]) {
																		translate(v = [9.95, 9.95, -11]) {
																			translate(v = [0, 0, -1.5]) {
																				cube(center = true, size = [0.1, 0.1, 3]);
																			}
																		}
																	}
																}
															}
														}
													}
												}
											}
										}
									}
								}
								translate(v = [0, 0, 30.5]) {
									rotate(a = 18.0, v = [1, 0, 0]) {
										rotate(a = 18.0, v = [0, 1, 0]) {
											translate(v = [0, 0, 3]) {
												translate(v = [0, 0, 230.49306344750678]) {
													rotate(a = 10.0, v = [0, 1, 0]) {
														translate(v = [0, 0, -230.49306344750678]) {
															translate(v = [0, 0, 79.73635378597841]) {
																rotate(a = 14.999999999999998, v = [1, 0, 0]) {
																	translate(v = [0, 0, -79.73635378597841]) {
																		translate(v = [9.95, -9.95, -11]) {
																			translate(v = [0, 0, -1.5]) {
																				cube(center = true, size = [0.1, 0.1, 3]);
																			}
																		}
																	}
																}
															}
														}
													}
												}
											}
										}
									}
								}
								translate(v = [0, 0, 30.5]) {
									rotate(a = 18.0, v = [1, 0, 0]) {
										rotate(a = 18.0, v = [0, 1, 0]) {
											translate(v = [0, 0, 3]) {
												translate(v = [0, 0, 230.49306344750678]) {
													rotate(a = 5.0, v = [0, 1, 0]) {
														translate(v = [0, 0, -230.49306344750678]) {
															translate(v = [0, 0, 79.73635378597841]) {
																rotate(a = 14.999999999999998, v = [1, 0, 0]) {
																	translate(v = [0, 0, -79.73635378597841]) {
																		translate(v = [-11.95, -9.95, -11]) {
																			translate(v = [0, 0, -1.5]) {
																				cube(center = true, size = [0.1, 0.1, 3]);
																			}
																		}
																	}
																}
															}
														}
													}
												}
											}
										}
									}
								}
							}
							hull() {
								translate(v = [0, 0, 30.5]) {
									rotate(a = 18.0, v = [1, 0, 0]) {
										rotate(a = 18.0, v = [0, 1, 0]) {
											translate(v = [0, 0, 3]) {
												translate(v = [0, 6.82, -4.0]) {
													translate(v = [0, 0, 230.49306344750678]) {
														rotate(a = 0.0, v = [0, 1, 0]) {
															translate(v = [0, 0, -230.49306344750678]) {
																translate(v = [0, 0, 79.73635378597841]) {
																	rotate(a = 0.0, v = [1, 0, 0]) {
																		translate(v = [0, 0, -79.73635378597841]) {
																			translate(v = [-10.95, 9.95, -11]) {
																				translate(v = [0, 0, -1.5]) {
																					cube(center = true, size = [0.1, 0.1, 3]);
																				}
																			}
																		}
																	}
																}
															}
														}
													}
												}
											}
										}
									}
								}
								translate(v = [0, 0, 30.5]) {
									rotate(a = 18.0, v = [1, 0, 0]) {
										rotate(a = 18.0, v = [0, 1, 0]) {
											translate(v = [0, 0, 3]) {
												translate(v = [0, 0, 230.49306344750678]) {
													rotate(a = 5.0, v = [0, 1, 0]) {
														translate(v = [0, 0, -230.49306344750678]) {
															translate(v = [0, 0, 79.73635378597841]) {
																rotate(a = 0.0, v = [1, 0, 0]) {
																	translate(v = [0, 0, -79.73635378597841]) {
																		translate(v = [7.949999999999999, 9.95, -11]) {
																			translate(v = [0, 0, -1.5]) {
																				cube(center = true, size = [0.1, 0.1, 3]);
																			}
																		}
																	}
																}
															}
														}
													}
												}
											}
										}
									}
								}
								translate(v = [0, 0, 30.5]) {
									rotate(a = 18.0, v = [1, 0, 0]) {
										rotate(a = 18.0, v = [0, 1, 0]) {
											translate(v = [0, 0, 3]) {
												translate(v = [0, 0, 230.49306344750678]) {
													rotate(a = 5.0, v = [0, 1, 0]) {
														translate(v = [0, 0, -230.49306344750678]) {
															translate(v = [0, 0, 79.73635378597841]) {
																rotate(a = 14.999999999999998, v = [1, 0, 0]) {
																	translate(v = [0, 0, -79.73635378597841]) {
																		translate(v = [7.949999999999999, -9.95, -11]) {
																			translate(v = [0, 0, -1.5]) {
																				cube(center = true, size = [0.1, 0.1, 3]);
																			}
																		}
																	}
																}
															}
														}
													}
												}
											}
										}
									}
								}
								translate(v = [0, 0, 30.5]) {
									rotate(a = 18.0, v = [1, 0, 0]) {
										rotate(a = 18.0, v = [0, 1, 0]) {
											translate(v = [0, 0, 3]) {
												translate(v = [0, 6.82, -4.0]) {
													translate(v = [0, 0, 230.49306344750678]) {
														rotate(a = 0.0, v = [0, 1, 0]) {
															translate(v = [0, 0, -230.49306344750678]) {
																translate(v = [0, 0, 79.73635378597841]) {
																	rotate(a = 14.999999999999998, v = [1, 0, 0]) {
																		translate(v = [0, 0, -79.73635378597841]) {
																			translate(v = [-10.95, -9.95, -11]) {
																				translate(v = [0, 0, -1.5]) {
																					cube(center = true, size = [0.1, 0.1, 3]);
																				}
																			}
																		}
																	}
																}
															}
														}
													}
												}
											}
										}
									}
								}
							}
							hull() {
								translate(v = [0, 0, 30.5]) {
									rotate(a = 18.0, v = [1, 0, 0]) {
										rotate(a = 18.0, v = [0, 1, 0]) {
											translate(v = [0, 0, 3]) {
												translate(v = [0, 0, 230.49306344750678]) {
													rotate(a = -5.0, v = [0, 1, 0]) {
														translate(v = [0, 0, -230.49306344750678]) {
															translate(v = [0, 0, 79.73635378597841]) {
																rotate(a = 0.0, v = [1, 0, 0]) {
																	translate(v = [0, 0, -79.73635378597841]) {
																		translate(v = [-7.949999999999999, 9.95, -11]) {
																			translate(v = [0, 0, -1.5]) {
																				cube(center = true, size = [0.1, 0.1, 3]);
																			}
																		}
																	}
																}
															}
														}
													}
												}
											}
										}
									}
								}
								translate(v = [0, 0, 30.5]) {
									rotate(a = 18.0, v = [1, 0, 0]) {
										rotate(a = 18.0, v = [0, 1, 0]) {
											translate(v = [0, 0, 3]) {
												translate(v = [0, 6.82, -4.0]) {
													translate(v = [0, 0, 230.49306344750678]) {
														rotate(a = 0.0, v = [0, 1, 0]) {
															translate(v = [0, 0, -230.49306344750678]) {
																translate(v = [0, 0, 79.73635378597841]) {
																	rotate(a = 0.0, v = [1, 0, 0]) {
																		translate(v = [0, 0, -79.73635378597841]) {
																			translate(v = [10.95, 9.95, -11]) {
																				translate(v = [0, 0, -1.5]) {
																					cube(center = true, size = [0.1, 0.1, 3]);
																				}
																			}
																		}
																	}
																}
															}
														}
													}
												}
											}
										}
									}
								}
								translate(v = [0, 0, 30.5]) {
									rotate(a = 18.0, v = [1, 0, 0]) {
										rotate(a = 18.0, v = [0, 1, 0]) {
											translate(v = [0, 0, 3]) {
												translate(v = [0, 6.82, -4.0]) {
													translate(v = [0, 0, 230.49306344750678]) {
														rotate(a = 0.0, v = [0, 1, 0]) {
															translate(v = [0, 0, -230.49306344750678]) {
																translate(v = [0, 0, 79.73635378597841]) {
																	rotate(a = 14.999999999999998, v = [1, 0, 0]) {
																		translate(v = [0, 0, -79.73635378597841]) {
																			translate(v = [10.95, -9.95, -11]) {
																				translate(v = [0, 0, -1.5]) {
																					cube(center = true, size = [0.1, 0.1, 3]);
																				}
																			}
																		}
																	}
																}
															}
														}
													}
												}
											}
										}
									}
								}
								translate(v = [0, 0, 30.5]) {
									rotate(a = 18.0, v = [1, 0, 0]) {
										rotate(a = 18.0, v = [0, 1, 0]) {
											translate(v = [0, 0, 3]) {
												translate(v = [0, 0, 230.49306344750678]) {
													rotate(a = -5.0, v = [0, 1, 0]) {
														translate(v = [0, 0, -230.49306344750678]) {
															translate(v = [0, 0, 79.73635378597841]) {
																rotate(a = 14.999999999999998, v = [1, 0, 0]) {
																	translate(v = [0, 0, -79.73635378597841]) {
																		translate(v = [-7.949999999999999, -9.95, -11]) {
																			translate(v = [0, 0, -1.5]) {
																				cube(center = true, size = [0.1, 0.1, 3]);
																			}
																		}
																	}
																}
															}
														}
													}
												}
											}
										}
									}
								}
							}
							hull() {
								translate(v = [0, 0, 30.5]) {
									rotate(a = 18.0, v = [1, 0, 0]) {
										rotate(a = 18.0, v = [0, 1, 0]) {
											translate(v = [0, 0, 3]) {
												translate(v = [0, -20.8, 7.64]) {
													translate(v = [0, 0, 230.49306344750678]) {
														rotate(a = -10.0, v = [0, 1, 0]) {
															translate(v = [0, 0, -230.49306344750678]) {
																translate(v = [0, 0, 79.73635378597841]) {
																	rotate(a = 0.0, v = [1, 0, 0]) {
																		translate(v = [0, 0, -79.73635378597841]) {
																			translate(v = [-6.949999999999999, 9.95, -11]) {
																				translate(v = [0, 0, -1.5]) {
																					cube(center = true, size = [0.1, 0.1, 3]);
																				}
																			}
																		}
																	}
																}
															}
														}
													}
												}
											}
										}
									}
								}
								translate(v = [0, 0, 30.5]) {
									rotate(a = 18.0, v = [1, 0, 0]) {
										rotate(a = 18.0, v = [0, 1, 0]) {
											translate(v = [0, 0, 3]) {
												translate(v = [0, 0, 230.49306344750678]) {
													rotate(a = -5.0, v = [0, 1, 0]) {
														translate(v = [0, 0, -230.49306344750678]) {
															translate(v = [0, 0, 79.73635378597841]) {
																rotate(a = 0.0, v = [1, 0, 0]) {
																	translate(v = [0, 0, -79.73635378597841]) {
																		translate(v = [11.95, 9.95, -11]) {
																			translate(v = [0, 0, -1.5]) {
																				cube(center = true, size = [0.1, 0.1, 3]);
																			}
																		}
																	}
																}
															}
														}
													}
												}
											}
										}
									}
								}
								translate(v = [0, 0, 30.5]) {
									rotate(a = 18.0, v = [1, 0, 0]) {
										rotate(a = 18.0, v = [0, 1, 0]) {
											translate(v = [0, 0, 3]) {
												translate(v = [0, 0, 230.49306344750678]) {
													rotate(a = -5.0, v = [0, 1, 0]) {
														translate(v = [0, 0, -230.49306344750678]) {
															translate(v = [0, 0, 79.73635378597841]) {
																rotate(a = 14.999999999999998, v = [1, 0, 0]) {
																	translate(v = [0, 0, -79.73635378597841]) {
																		translate(v = [11.95, -9.95, -11]) {
																			translate(v = [0, 0, -1.5]) {
																				cube(center = true, size = [0.1, 0.1, 3]);
																			}
																		}
																	}
																}
															}
														}
													}
												}
											}
										}
									}
								}
								translate(v = [0, 0, 30.5]) {
									rotate(a = 18.0, v = [1, 0, 0]) {
										rotate(a = 18.0, v = [0, 1, 0]) {
											translate(v = [0, 0, 3]) {
												translate(v = [0, -20.8, 7.64]) {
													translate(v = [0, 0, 230.49306344750678]) {
														rotate(a = -10.0, v = [0, 1, 0]) {
															translate(v = [0, 0, -230.49306344750678]) {
																translate(v = [0, 0, 79.73635378597841]) {
																	rotate(a = 14.999999999999998, v = [1, 0, 0]) {
																		translate(v = [0, 0, -79.73635378597841]) {
																			translate(v = [-6.949999999999999, -9.95, -11]) {
																				translate(v = [0, 0, -1.5]) {
																					cube(center = true, size = [0.1, 0.1, 3]);
																				}
																			}
																		}
																	}
																}
															}
														}
													}
												}
											}
										}
									}
								}
							}
							hull() {
								translate(v = [0, 0, 30.5]) {
									rotate(a = 18.0, v = [1, 0, 0]) {
										rotate(a = 18.0, v = [0, 1, 0]) {
											translate(v = [0, 0, 3]) {
												translate(v = [0, -20.8, 7.64]) {
													translate(v = [0, 0, 230.49306344750678]) {
														rotate(a = -14.999999999999998, v = [0, 1, 0]) {
															translate(v = [0, 0, -230.49306344750678]) {
																translate(v = [0, 0, 79.73635378597841]) {
																	rotate(a = 0.0, v = [1, 0, 0]) {
																		translate(v = [0, 0, -79.73635378597841]) {
																			translate(v = [-9.95, 9.95, -11]) {
																				translate(v = [0, 0, -1.5]) {
																					cube(center = true, size = [0.1, 0.1, 3]);
																				}
																			}
																		}
																	}
																}
															}
														}
													}
												}
											}
										}
									}
								}
								translate(v = [0, 0, 30.5]) {
									rotate(a = 18.0, v = [1, 0, 0]) {
										rotate(a = 18.0, v = [0, 1, 0]) {
											translate(v = [0, 0, 3]) {
												translate(v = [0, -20.8, 7.64]) {
													translate(v = [0, 0, 230.49306344750678]) {
														rotate(a = -10.0, v = [0, 1, 0]) {
															translate(v = [0, 0, -230.49306344750678]) {
																translate(v = [0, 0, 79.73635378597841]) {
																	rotate(a = 0.0, v = [1, 0, 0]) {
																		translate(v = [0, 0, -79.73635378597841]) {
																			translate(v = [10.95, 9.95, -11]) {
																				translate(v = [0, 0, -1.5]) {
																					cube(center = true, size = [0.1, 0.1, 3]);
																				}
																			}
																		}
																	}
																}
															}
														}
													}
												}
											}
										}
									}
								}
								translate(v = [0, 0, 30.5]) {
									rotate(a = 18.0, v = [1, 0, 0]) {
										rotate(a = 18.0, v = [0, 1, 0]) {
											translate(v = [0, 0, 3]) {
												translate(v = [0, -20.8, 7.64]) {
													translate(v = [0, 0, 230.49306344750678]) {
														rotate(a = -10.0, v = [0, 1, 0]) {
															translate(v = [0, 0, -230.49306344750678]) {
																translate(v = [0, 0, 79.73635378597841]) {
																	rotate(a = 14.999999999999998, v = [1, 0, 0]) {
																		translate(v = [0, 0, -79.73635378597841]) {
																			translate(v = [10.95, -9.95, -11]) {
																				translate(v = [0, 0, -1.5]) {
																					cube(center = true, size = [0.1, 0.1, 3]);
																				}
																			}
																		}
																	}
																}
															}
														}
													}
												}
											}
										}
									}
								}
								translate(v = [0, 0, 30.5]) {
									rotate(a = 18.0, v = [1, 0, 0]) {
										rotate(a = 18.0, v = [0, 1, 0]) {
											translate(v = [0, 0, 3]) {
												translate(v = [0, -20.8, 7.64]) {
													translate(v = [0, 0, 230.49306344750678]) {
														rotate(a = -14.999999999999998, v = [0, 1, 0]) {
															translate(v = [0, 0, -230.49306344750678]) {
																translate(v = [0, 0, 79.73635378597841]) {
																	rotate(a = 14.999999999999998, v = [1, 0, 0]) {
																		translate(v = [0, 0, -79.73635378597841]) {
																			translate(v = [-9.95, -9.95, -11]) {
																				translate(v = [0, 0, -1.5]) {
																					cube(center = true, size = [0.1, 0.1, 3]);
																				}
																			}
																		}
																	}
																}
															}
														}
													}
												}
											}
										}
									}
								}
							}
							hull() {
								translate(v = [0, 0, 30.5]) {
									rotate(a = 18.0, v = [1, 0, 0]) {
										rotate(a = 18.0, v = [0, 1, 0]) {
											translate(v = [0, 0, 3]) {
												translate(v = [0, 0, 230.49306344750678]) {
													rotate(a = 5.0, v = [0, 1, 0]) {
														translate(v = [0, 0, -230.49306344750678]) {
															translate(v = [0, 0, 79.73635378597841]) {
																rotate(a = -14.999999999999998, v = [1, 0, 0]) {
																	translate(v = [0, 0, -79.73635378597841]) {
																		translate(v = [-11.95, 9.95, -11]) {
																			translate(v = [0, 0, -1.5]) {
																				cube(center = true, size = [0.1, 0.1, 3]);
																			}
																		}
																	}
																}
															}
														}
													}
												}
											}
										}
									}
								}
								translate(v = [0, 0, 30.5]) {
									rotate(a = 18.0, v = [1, 0, 0]) {
										rotate(a = 18.0, v = [0, 1, 0]) {
											translate(v = [0, 0, 3]) {
												translate(v = [0, 0, 230.49306344750678]) {
													rotate(a = 10.0, v = [0, 1, 0]) {
														translate(v = [0, 0, -230.49306344750678]) {
															translate(v = [0, 0, 79.73635378597841]) {
																rotate(a = -14.999999999999998, v = [1, 0, 0]) {
																	translate(v = [0, 0, -79.73635378597841]) {
																		translate(v = [9.95, 9.95, -11]) {
																			translate(v = [0, 0, -1.5]) {
																				cube(center = true, size = [0.1, 0.1, 3]);
																			}
																		}
																	}
																}
															}
														}
													}
												}
											}
										}
									}
								}
								translate(v = [0, 0, 30.5]) {
									rotate(a = 18.0, v = [1, 0, 0]) {
										rotate(a = 18.0, v = [0, 1, 0]) {
											translate(v = [0, 0, 3]) {
												translate(v = [0, 0, 230.49306344750678]) {
													rotate(a = 10.0, v = [0, 1, 0]) {
														translate(v = [0, 0, -230.49306344750678]) {
															translate(v = [0, 0, 79.73635378597841]) {
																rotate(a = 0.0, v = [1, 0, 0]) {
																	translate(v = [0, 0, -79.73635378597841]) {
																		translate(v = [9.95, -9.95, -11]) {
																			translate(v = [0, 0, -1.5]) {
																				cube(center = true, size = [0.1, 0.1, 3]);
																			}
																		}
																	}
																}
															}
														}
													}
												}
											}
										}
									}
								}
								translate(v = [0, 0, 30.5]) {
									rotate(a = 18.0, v = [1, 0, 0]) {
										rotate(a = 18.0, v = [0, 1, 0]) {
											translate(v = [0, 0, 3]) {
												translate(v = [0, 0, 230.49306344750678]) {
													rotate(a = 5.0, v = [0, 1, 0]) {
														translate(v = [0, 0, -230.49306344750678]) {
															translate(v = [0, 0, 79.73635378597841]) {
																rotate(a = 0.0, v = [1, 0, 0]) {
																	translate(v = [0, 0, -79.73635378597841]) {
																		translate(v = [-11.95, -9.95, -11]) {
																			translate(v = [0, 0, -1.5]) {
																				cube(center = true, size = [0.1, 0.1, 3]);
																			}
																		}
																	}
																}
															}
														}
													}
												}
											}
										}
									}
								}
							}
							hull() {
								translate(v = [0, 0, 30.5]) {
									rotate(a = 18.0, v = [1, 0, 0]) {
										rotate(a = 18.0, v = [0, 1, 0]) {
											translate(v = [0, 0, 3]) {
												translate(v = [0, 6.82, -4.0]) {
													translate(v = [0, 0, 230.49306344750678]) {
														rotate(a = 0.0, v = [0, 1, 0]) {
															translate(v = [0, 0, -230.49306344750678]) {
																translate(v = [0, 0, 79.73635378597841]) {
																	rotate(a = -14.999999999999998, v = [1, 0, 0]) {
																		translate(v = [0, 0, -79.73635378597841]) {
																			translate(v = [-10.95, 9.95, -11]) {
																				translate(v = [0, 0, -1.5]) {
																					cube(center = true, size = [0.1, 0.1, 3]);
																				}
																			}
																		}
																	}
																}
															}
														}
													}
												}
											}
										}
									}
								}
								translate(v = [0, 0, 30.5]) {
									rotate(a = 18.0, v = [1, 0, 0]) {
										rotate(a = 18.0, v = [0, 1, 0]) {
											translate(v = [0, 0, 3]) {
												translate(v = [0, 0, 230.49306344750678]) {
													rotate(a = 5.0, v = [0, 1, 0]) {
														translate(v = [0, 0, -230.49306344750678]) {
															translate(v = [0, 0, 79.73635378597841]) {
																rotate(a = -14.999999999999998, v = [1, 0, 0]) {
																	translate(v = [0, 0, -79.73635378597841]) {
																		translate(v = [7.949999999999999, 9.95, -11]) {
																			translate(v = [0, 0, -1.5]) {
																				cube(center = true, size = [0.1, 0.1, 3]);
																			}
																		}
																	}
																}
															}
														}
													}
												}
											}
										}
									}
								}
								translate(v = [0, 0, 30.5]) {
									rotate(a = 18.0, v = [1, 0, 0]) {
										rotate(a = 18.0, v = [0, 1, 0]) {
											translate(v = [0, 0, 3]) {
												translate(v = [0, 0, 230.49306344750678]) {
													rotate(a = 5.0, v = [0, 1, 0]) {
														translate(v = [0, 0, -230.49306344750678]) {
															translate(v = [0, 0, 79.73635378597841]) {
																rotate(a = 0.0, v = [1, 0, 0]) {
																	translate(v = [0, 0, -79.73635378597841]) {
																		translate(v = [7.949999999999999, -9.95, -11]) {
																			translate(v = [0, 0, -1.5]) {
																				cube(center = true, size = [0.1, 0.1, 3]);
																			}
																		}
																	}
																}
															}
														}
													}
												}
											}
										}
									}
								}
								translate(v = [0, 0, 30.5]) {
									rotate(a = 18.0, v = [1, 0, 0]) {
										rotate(a = 18.0, v = [0, 1, 0]) {
											translate(v = [0, 0, 3]) {
												translate(v = [0, 6.82, -4.0]) {
													translate(v = [0, 0, 230.49306344750678]) {
														rotate(a = 0.0, v = [0, 1, 0]) {
															translate(v = [0, 0, -230.49306344750678]) {
																translate(v = [0, 0, 79.73635378597841]) {
																	rotate(a = 0.0, v = [1, 0, 0]) {
																		translate(v = [0, 0, -79.73635378597841]) {
																			translate(v = [-10.95, -9.95, -11]) {
																				translate(v = [0, 0, -1.5]) {
																					cube(center = true, size = [0.1, 0.1, 3]);
																				}
																			}
																		}
																	}
																}
															}
														}
													}
												}
											}
										}
									}
								}
							}
							hull() {
								translate(v = [0, 0, 30.5]) {
									rotate(a = 18.0, v = [1, 0, 0]) {
										rotate(a = 18.0, v = [0, 1, 0]) {
											translate(v = [0, 0, 3]) {
												translate(v = [0, 0, 230.49306344750678]) {
													rotate(a = -5.0, v = [0, 1, 0]) {
														translate(v = [0, 0, -230.49306344750678]) {
															translate(v = [0, 0, 79.73635378597841]) {
																rotate(a = -14.999999999999998, v = [1, 0, 0]) {
																	translate(v = [0, 0, -79.73635378597841]) {
																		translate(v = [-7.949999999999999, 9.95, -11]) {
																			translate(v = [0, 0, -1.5]) {
																				cube(center = true, size = [0.1, 0.1, 3]);
																			}
																		}
																	}
																}
															}
														}
													}
												}
											}
										}
									}
								}
								translate(v = [0, 0, 30.5]) {
									rotate(a = 18.0, v = [1, 0, 0]) {
										rotate(a = 18.0, v = [0, 1, 0]) {
											translate(v = [0, 0, 3]) {
												translate(v = [0, 6.82, -4.0]) {
													translate(v = [0, 0, 230.49306344750678]) {
														rotate(a = 0.0, v = [0, 1, 0]) {
															translate(v = [0, 0, -230.49306344750678]) {
																translate(v = [0, 0, 79.73635378597841]) {
																	rotate(a = -14.999999999999998, v = [1, 0, 0]) {
																		translate(v = [0, 0, -79.73635378597841]) {
																			translate(v = [10.95, 9.95, -11]) {
																				translate(v = [0, 0, -1.5]) {
																					cube(center = true, size = [0.1, 0.1, 3]);
																				}
																			}
																		}
																	}
																}
															}
														}
													}
												}
											}
										}
									}
								}
								translate(v = [0, 0, 30.5]) {
									rotate(a = 18.0, v = [1, 0, 0]) {
										rotate(a = 18.0, v = [0, 1, 0]) {
											translate(v = [0, 0, 3]) {
												translate(v = [0, 6.82, -4.0]) {
													translate(v = [0, 0, 230.49306344750678]) {
														rotate(a = 0.0, v = [0, 1, 0]) {
															translate(v = [0, 0, -230.49306344750678]) {
																translate(v = [0, 0, 79.73635378597841]) {
																	rotate(a = 0.0, v = [1, 0, 0]) {
																		translate(v = [0, 0, -79.73635378597841]) {
																			translate(v = [10.95, -9.95, -11]) {
																				translate(v = [0, 0, -1.5]) {
																					cube(center = true, size = [0.1, 0.1, 3]);
																				}
																			}
																		}
																	}
																}
															}
														}
													}
												}
											}
										}
									}
								}
								translate(v = [0, 0, 30.5]) {
									rotate(a = 18.0, v = [1, 0, 0]) {
										rotate(a = 18.0, v = [0, 1, 0]) {
											translate(v = [0, 0, 3]) {
												translate(v = [0, 0, 230.49306344750678]) {
													rotate(a = -5.0, v = [0, 1, 0]) {
														translate(v = [0, 0, -230.49306344750678]) {
															translate(v = [0, 0, 79.73635378597841]) {
																rotate(a = 0.0, v = [1, 0, 0]) {
																	translate(v = [0, 0, -79.73635378597841]) {
																		translate(v = [-7.949999999999999, -9.95, -11]) {
																			translate(v = [0, 0, -1.5]) {
																				cube(center = true, size = [0.1, 0.1, 3]);
																			}
																		}
																	}
																}
															}
														}
													}
												}
											}
										}
									}
								}
							}
							hull() {
								translate(v = [0, 0, 30.5]) {
									rotate(a = 18.0, v = [1, 0, 0]) {
										rotate(a = 18.0, v = [0, 1, 0]) {
											translate(v = [0, 0, 3]) {
												translate(v = [0, -20.8, 7.64]) {
													translate(v = [0, 0, 230.49306344750678]) {
														rotate(a = -10.0, v = [0, 1, 0]) {
															translate(v = [0, 0, -230.49306344750678]) {
																translate(v = [0, 0, 79.73635378597841]) {
																	rotate(a = -14.999999999999998, v = [1, 0, 0]) {
																		translate(v = [0, 0, -79.73635378597841]) {
																			translate(v = [-6.949999999999999, 9.95, -11]) {
																				translate(v = [0, 0, -1.5]) {
																					cube(center = true, size = [0.1, 0.1, 3]);
																				}
																			}
																		}
																	}
																}
															}
														}
													}
												}
											}
										}
									}
								}
								translate(v = [0, 0, 30.5]) {
									rotate(a = 18.0, v = [1, 0, 0]) {
										rotate(a = 18.0, v = [0, 1, 0]) {
											translate(v = [0, 0, 3]) {
												translate(v = [0, 0, 230.49306344750678]) {
													rotate(a = -5.0, v = [0, 1, 0]) {
														translate(v = [0, 0, -230.49306344750678]) {
															translate(v = [0, 0, 79.73635378597841]) {
																rotate(a = -14.999999999999998, v = [1, 0, 0]) {
																	translate(v = [0, 0, -79.73635378597841]) {
																		translate(v = [11.95, 9.95, -11]) {
																			translate(v = [0, 0, -1.5]) {
																				cube(center = true, size = [0.1, 0.1, 3]);
																			}
																		}
																	}
																}
															}
														}
													}
												}
											}
										}
									}
								}
								translate(v = [0, 0, 30.5]) {
									rotate(a = 18.0, v = [1, 0, 0]) {
										rotate(a = 18.0, v = [0, 1, 0]) {
											translate(v = [0, 0, 3]) {
												translate(v = [0, 0, 230.49306344750678]) {
													rotate(a = -5.0, v = [0, 1, 0]) {
														translate(v = [0, 0, -230.49306344750678]) {
															translate(v = [0, 0, 79.73635378597841]) {
																rotate(a = 0.0, v = [1, 0, 0]) {
																	translate(v = [0, 0, -79.73635378597841]) {
																		translate(v = [11.95, -9.95, -11]) {
																			translate(v = [0, 0, -1.5]) {
																				cube(center = true, size = [0.1, 0.1, 3]);
																			}
																		}
																	}
																}
															}
														}
													}
												}
											}
										}
									}
								}
								translate(v = [0, 0, 30.5]) {
									rotate(a = 18.0, v = [1, 0, 0]) {
										rotate(a = 18.0, v = [0, 1, 0]) {
											translate(v = [0, 0, 3]) {
												translate(v = [0, -20.8, 7.64]) {
													translate(v = [0, 0, 230.49306344750678]) {
														rotate(a = -10.0, v = [0, 1, 0]) {
															translate(v = [0, 0, -230.49306344750678]) {
																translate(v = [0, 0, 79.73635378597841]) {
																	rotate(a = 0.0, v = [1, 0, 0]) {
																		translate(v = [0, 0, -79.73635378597841]) {
																			translate(v = [-6.949999999999999, -9.95, -11]) {
																				translate(v = [0, 0, -1.5]) {
																					cube(center = true, size = [0.1, 0.1, 3]);
																				}
																			}
																		}
																	}
																}
															}
														}
													}
												}
											}
										}
									}
								}
							}
							hull() {
								translate(v = [0, 0, 30.5]) {
									rotate(a = 18.0, v = [1, 0, 0]) {
										rotate(a = 18.0, v = [0, 1, 0]) {
											translate(v = [0, 0, 3]) {
												translate(v = [0, -20.8, 7.64]) {
													translate(v = [0, 0, 230.49306344750678]) {
														rotate(a = -14.999999999999998, v = [0, 1, 0]) {
															translate(v = [0, 0, -230.49306344750678]) {
																translate(v = [0, 0, 79.73635378597841]) {
																	rotate(a = -14.999999999999998, v = [1, 0, 0]) {
																		translate(v = [0, 0, -79.73635378597841]) {
																			translate(v = [-9.95, 9.95, -11]) {
																				translate(v = [0, 0, -1.5]) {
																					cube(center = true, size = [0.1, 0.1, 3]);
																				}
																			}
																		}
																	}
																}
															}
														}
													}
												}
											}
										}
									}
								}
								translate(v = [0, 0, 30.5]) {
									rotate(a = 18.0, v = [1, 0, 0]) {
										rotate(a = 18.0, v = [0, 1, 0]) {
											translate(v = [0, 0, 3]) {
												translate(v = [0, -20.8, 7.64]) {
													translate(v = [0, 0, 230.49306344750678]) {
														rotate(a = -10.0, v = [0, 1, 0]) {
															translate(v = [0, 0, -230.49306344750678]) {
																translate(v = [0, 0, 79.73635378597841]) {
																	rotate(a = -14.999999999999998, v = [1, 0, 0]) {
																		translate(v = [0, 0, -79.73635378597841]) {
																			translate(v = [10.95, 9.95, -11]) {
																				translate(v = [0, 0, -1.5]) {
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
